gogomaker/moodlight_HanClock/Design/External design/acrylic/덟.dxf

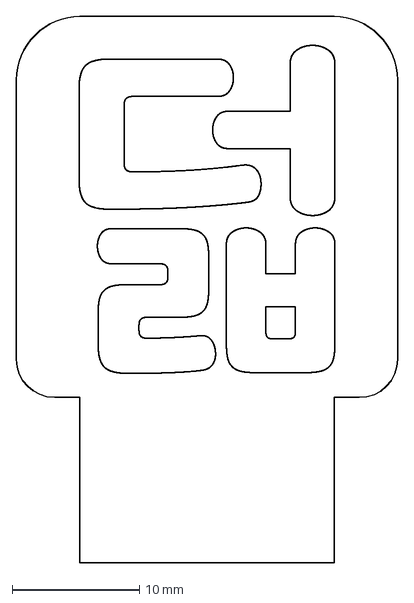
[picture p16: CAD file, 2021-06-14]
Design/External design/acrylic/덟.dxf
30.0 x 43.0 mm
