gogomaker/moodlight_HanClock/Design/External design/acrylic/시.dxf

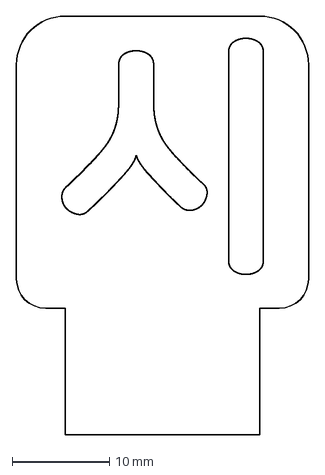
[picture p17: CAD file, 2021-06-14]
Design/External design/acrylic/시.dxf
30.0 x 43.0 mm
