gogomaker/moodlight_HanClock/Design/External design/acrylic/삼.dxf

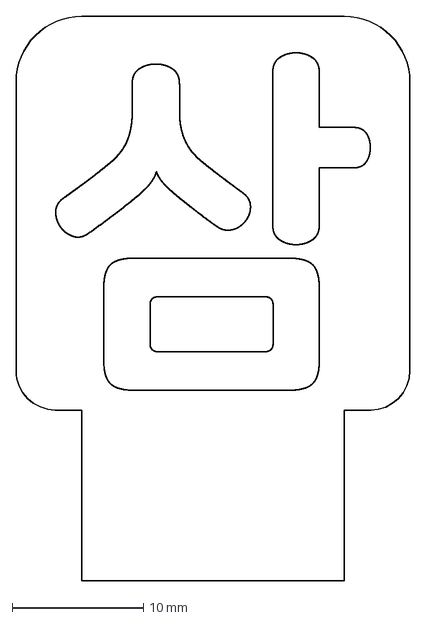
[picture p18: CAD file, 2021-06-14]
Design/External design/acrylic/삼.dxf
30.0 x 43.0 mm
