gogomaker/moodlight_HanClock/Design/External design/acrylic/칠.dxf

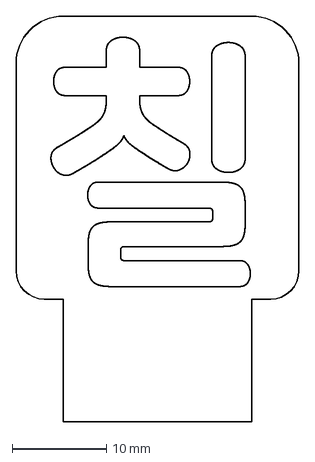
[picture p20: CAD file, 2021-06-14]
Design/External design/acrylic/칠.dxf
30.0 x 43.0 mm
