gogomaker/moodlight_HanClock/Design/External design/acrylic/십_2.dxf

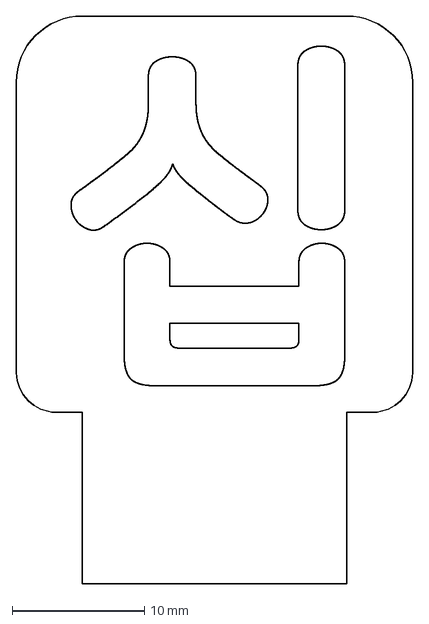
[picture p22: CAD file, 2021-06-14]
Design/External design/acrylic/십_2.dxf
30.0 x 43.0 mm
