gogomaker/moodlight_HanClock/Design/External design/acrylic/사_4.dxf

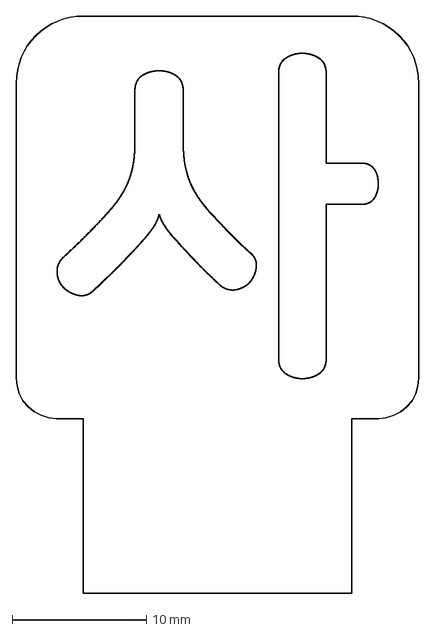
[picture p23: CAD file, 2021-06-14]
Design/External design/acrylic/사_4.dxf
30.0 x 43.0 mm
