gogomaker/moodlight_HanClock/Design/External design/acrylic/섯.dxf

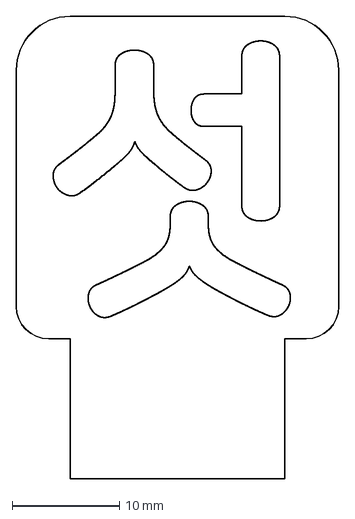
[picture p24: CAD file, 2021-06-14]
Design/External design/acrylic/섯.dxf
30.0 x 43.0 mm
