gogomaker/moodlight_HanClock/Design/External design/acrylic/네.dxf

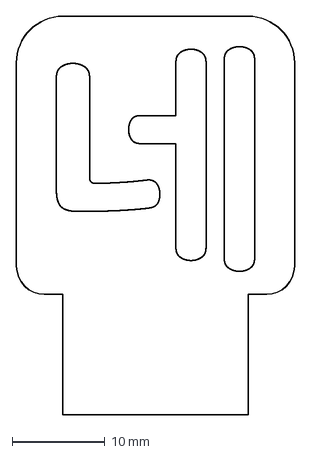
[picture p25: CAD file, 2021-06-14]
Design/External design/acrylic/네.dxf
30.0 x 43.0 mm
