gogomaker/moodlight_HanClock/Design/External design/acrylic/오.dxf

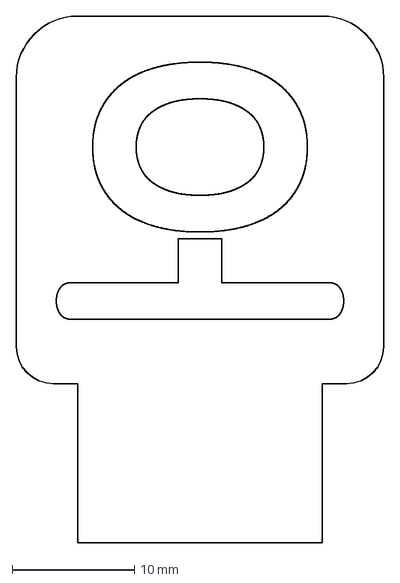
[picture p26: CAD file, 2021-06-14]
Design/External design/acrylic/오.dxf
30.0 x 43.0 mm
