gogomaker/moodlight_HanClock/Design/External design/acrylic/이.dxf

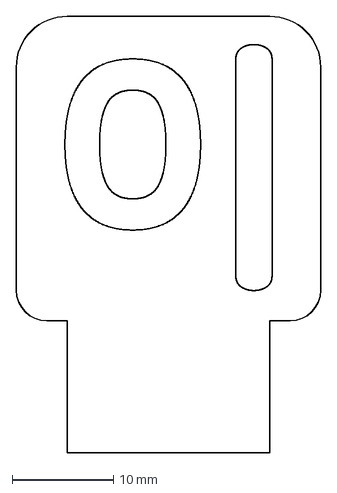
[picture p29: CAD file, 2021-06-14]
Design/External design/acrylic/이.dxf
30.0 x 43.0 mm
