gogomaker/moodlight_HanClock/Design/External design/acrylic/일_2.dxf

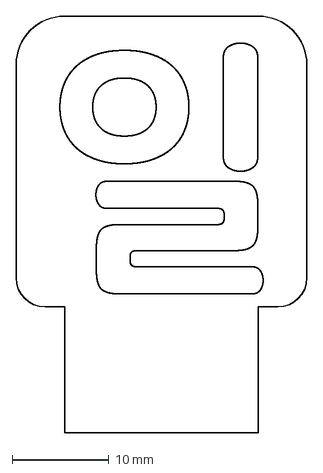
[picture p30: CAD file, 2021-06-14]
Design/External design/acrylic/일_2.dxf
30.0 x 43.0 mm
