gogomaker/moodlight_HanClock/Design/External design/acrylic/이_2.dxf

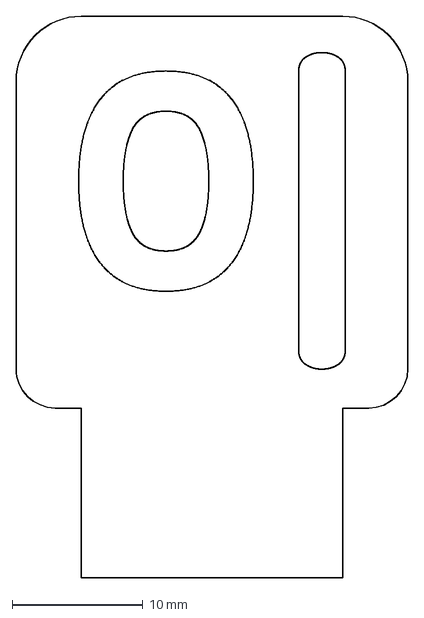
[picture p31: CAD file, 2021-06-14]
Design/External design/acrylic/이_2.dxf
30.0 x 43.0 mm
