gogomaker/moodlight_HanClock/Design/External design/acrylic/홉.dxf

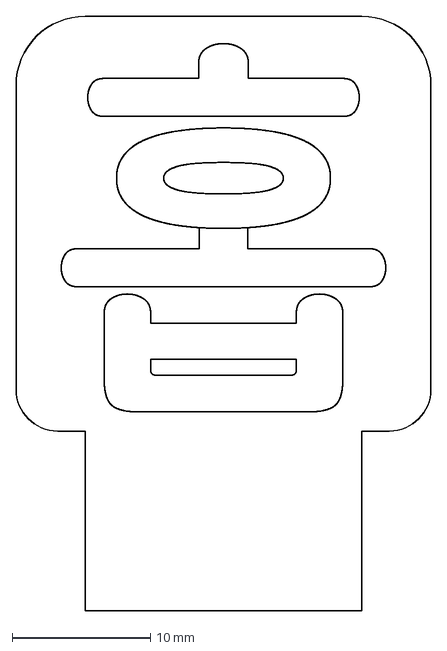
[picture p32: CAD file, 2021-06-14]
Design/External design/acrylic/홉.dxf
30.0 x 43.0 mm
