gogomaker/moodlight_HanClock/Design/External design/acrylic/사.dxf

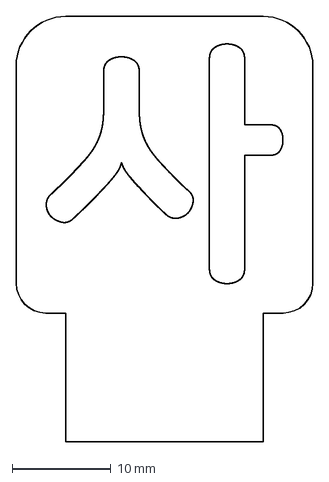
[picture p33: CAD file, 2021-06-14]
Design/External design/acrylic/사.dxf
30.0 x 43.0 mm
