gogomaker/moodlight_HanClock/Design/External design/acrylic/오_2.dxf

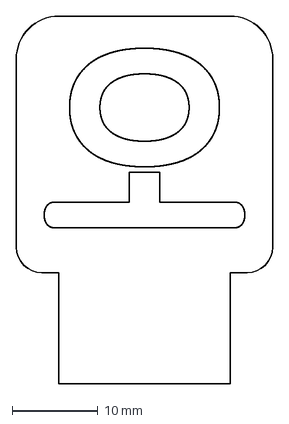
[picture p34: CAD file, 2021-06-14]
Design/External design/acrylic/오_2.dxf
30.0 x 43.0 mm
